charl56/Jukebox-V2/models/V3/Assemblage_cd.SLDASM

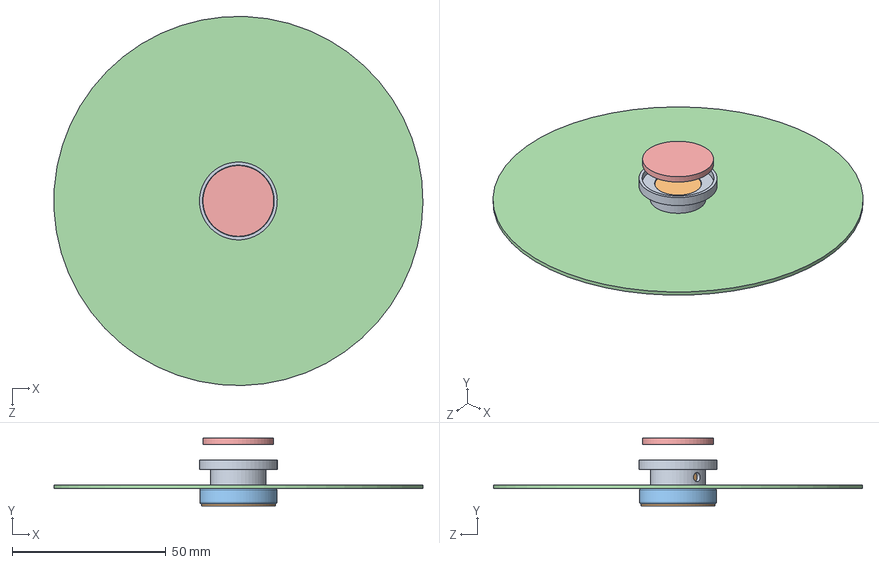
[picture p3: CAD file, 2025-11-25]
models/V3/Assemblage_cd.SLDASM
119.9 x 22.0 x 119.9 mm
Rondelle_prise
Cd_vide
Aimant
Support_cd_dos_aiamant_devant
Bouchon_aiamant_devant
