charl56/Jukebox-V2/models/V3/Assemblage_final.SLDASM

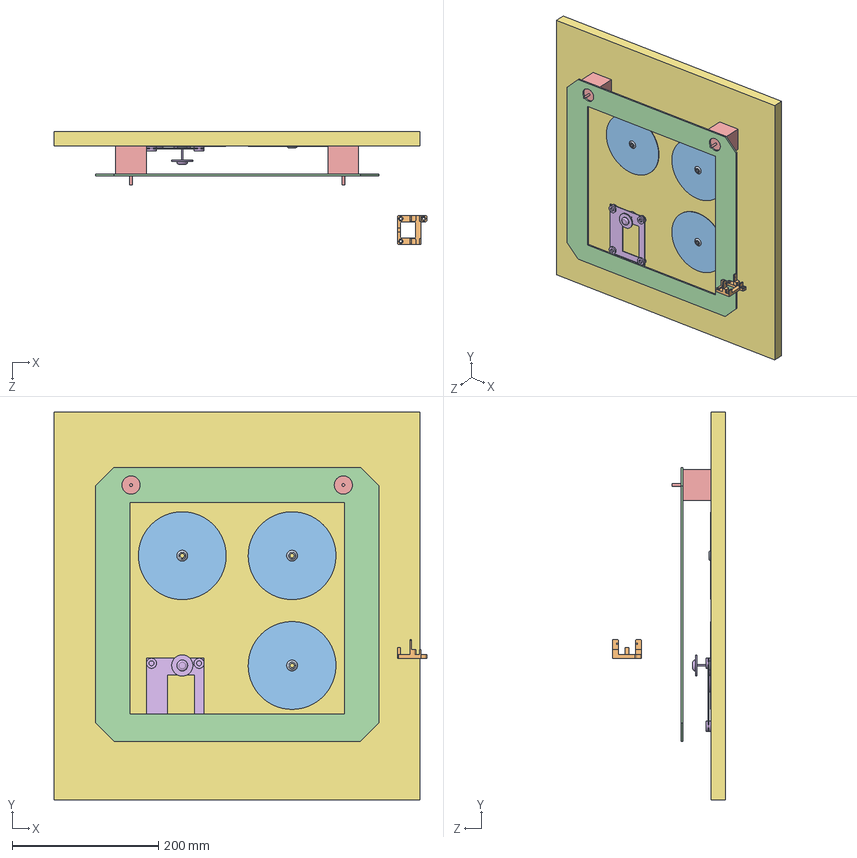
[picture p5: CAD file, 2025-11-25]
models/V3/Assemblage_final.SLDASM
509.1 x 530.0 x 154.8 mm
plaque
lecteur_cd_v2
moteur_pas_a_pas x 2
armature_moteurs
cd x 3
Support_elecaimant
support_cd_mur x 3
