charl56/Jukebox-V2/models/pinion_2.SLDPRT

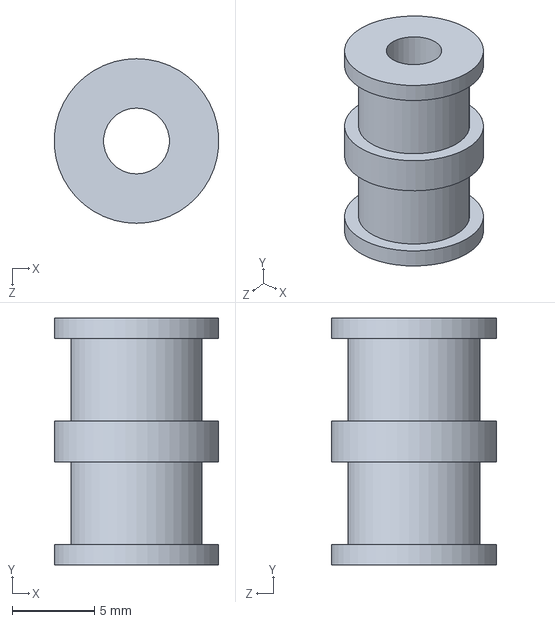
[picture p18: CAD file, 2025-04-08]
models/pinion_2.SLDPRT
9.98 x 15.0 x 10.0 mm
