charl56/Jukebox-V2/3d_models/nacelle_petite.SLDPRT

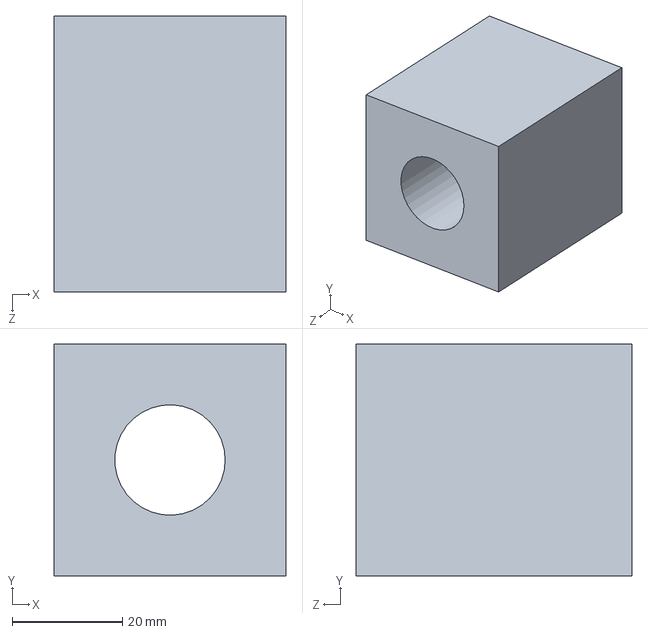
[picture p19: CAD file, 2024-03-14]
3d_models/nacelle_petite.SLDPRT
42.0 x 42.0 x 50.0 mm
