charl56/Jukebox-V2/models/rail.SLDPRT

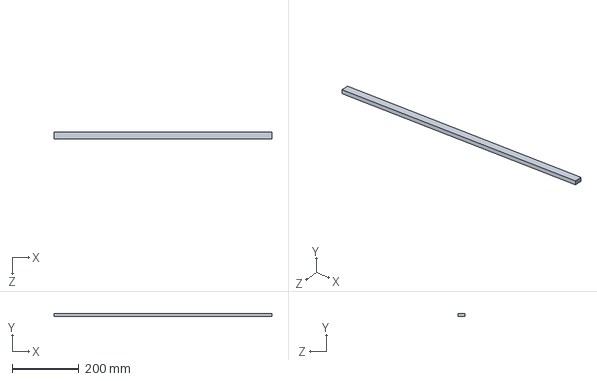
[picture p20: CAD file, 2025-04-08]
models/rail.SLDPRT
655.0 x 10.0 x 20.0 mm
