charl56/Jukebox-V2/models/V3/Bouchon_aiamant_devant.SLDPRT

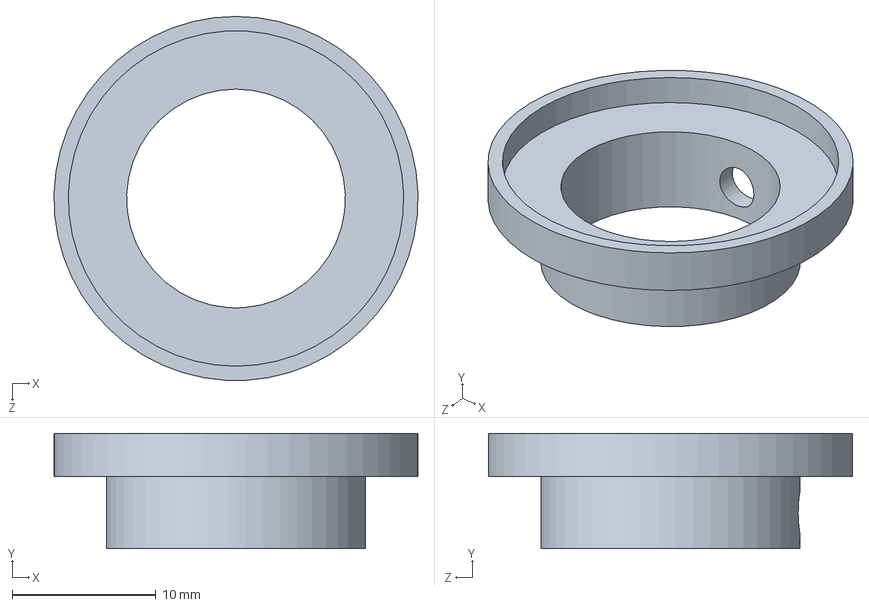
[picture p21: CAD file, 2025-11-25]
models/V3/Bouchon_aiamant_devant.SLDPRT
25.3 x 8.00 x 25.3 mm
