charl56/Jukebox-V2/models/plaque_plexi.SLDPRT

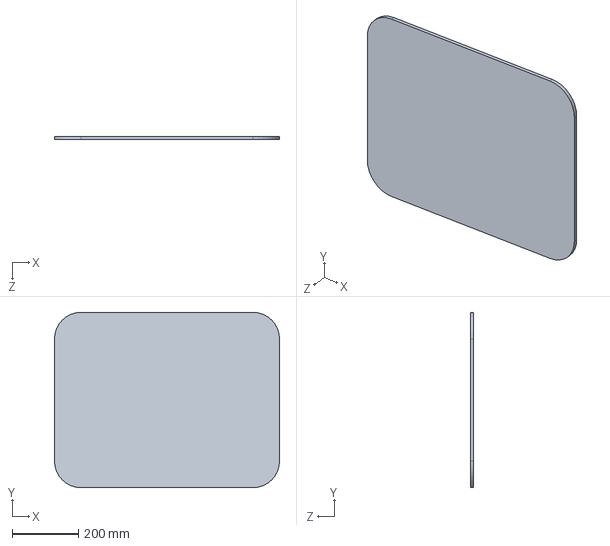
[picture p23: CAD file, 2025-04-08]
models/plaque_plexi.SLDPRT
680.0 x 530.0 x 10.0 mm
