charl56/Jukebox-V2/models/V3/armature_moteurs.SLDPRT

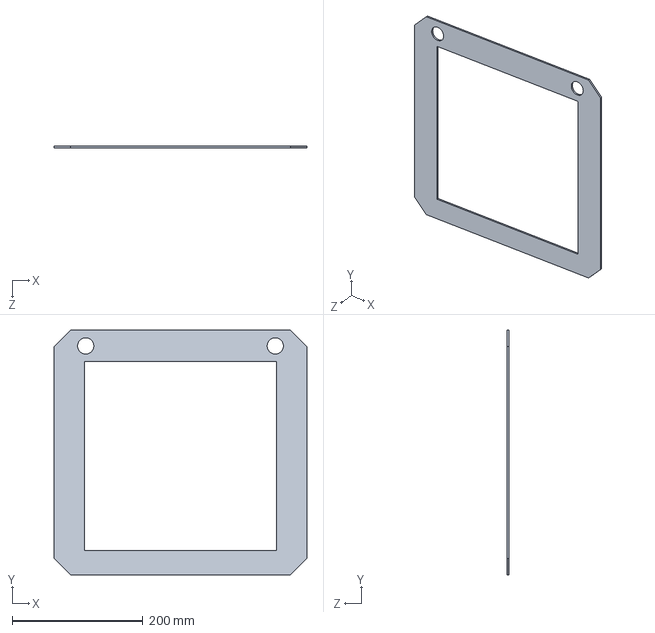
[picture p24: CAD file, 2025-11-25]
models/V3/armature_moteurs.SLDPRT
387.0 x 374.0 x 3.00 mm
