charl56/Jukebox-V2/3d_models/servo_fs90r.SLDPRT

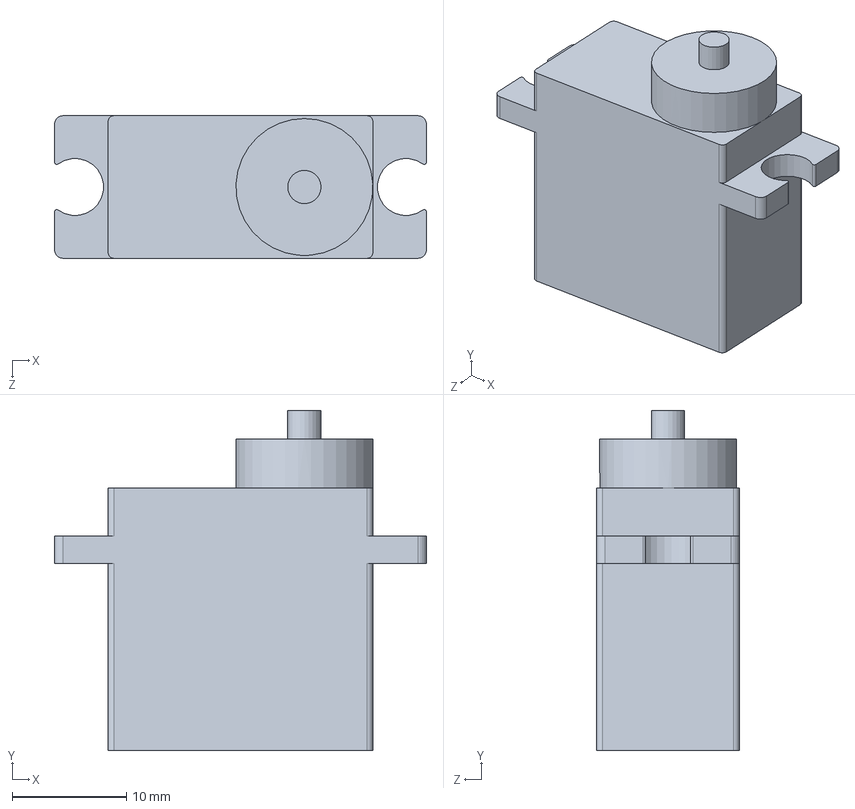
[picture p25: CAD file, 2024-03-14]
3d_models/servo_fs90r.SLDPRT
32.6 x 29.8 x 12.5 mm
