charl56/Jukebox-V2/models/lien_roulement_plateau_moteur_avec_accroches.SLDPRT

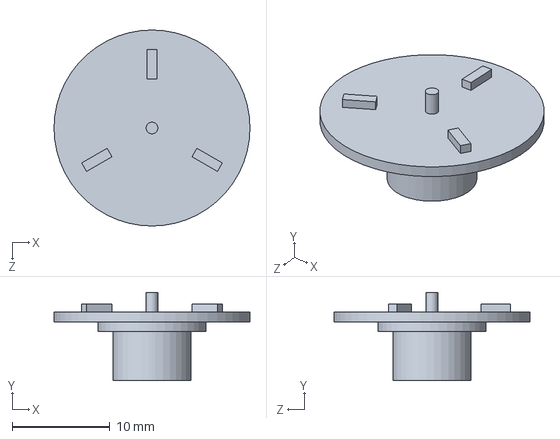
[picture p26: CAD file, 2025-04-08]
models/lien_roulement_plateau_moteur_avec_accroches.SLDPRT
20.0 x 9.00 x 20.0 mm
