charl56/Jukebox-V2/models/V3/support_cd_mur.SLDPRT

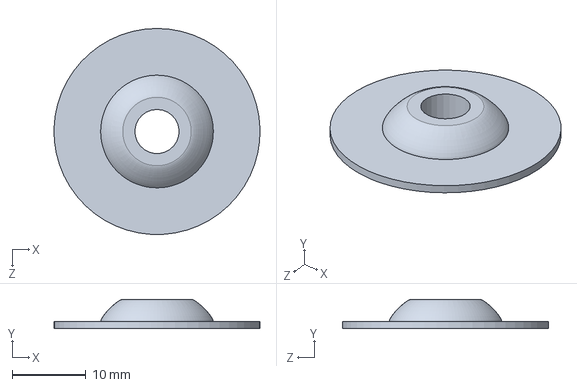
[picture p27: CAD file, 2025-11-25]
models/V3/support_cd_mur.SLDPRT
28.0 x 4.00 x 28.0 mm
