charl56/Jukebox-V2/3d_models/tige_filetee_petite.SLDPRT

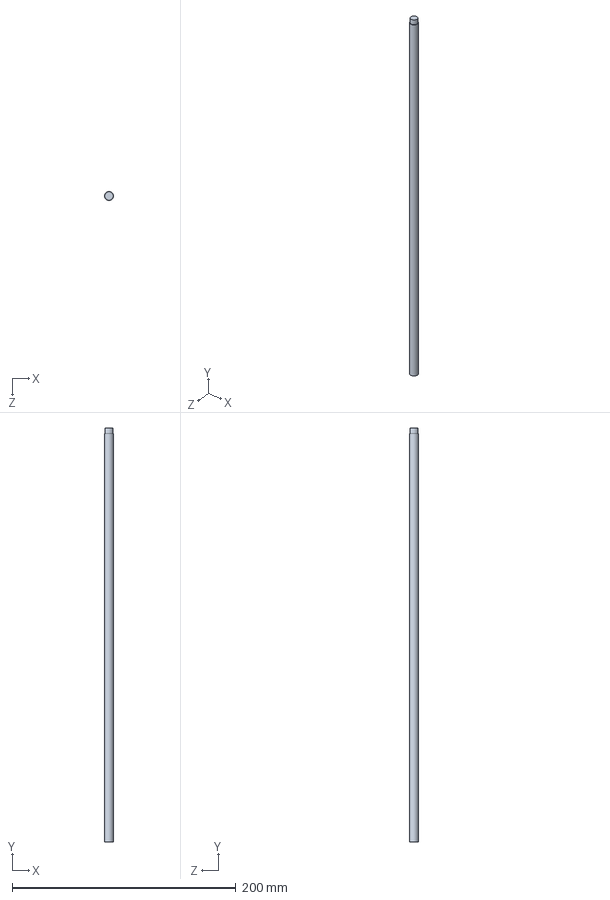
[picture p28: CAD file, 2024-03-14]
3d_models/tige_filetee_petite.SLDPRT
8.00 x 370.0 x 8.00 mm
