charl56/Jukebox-V2/models/lien_roulement_plateau_moteur.SLDPRT

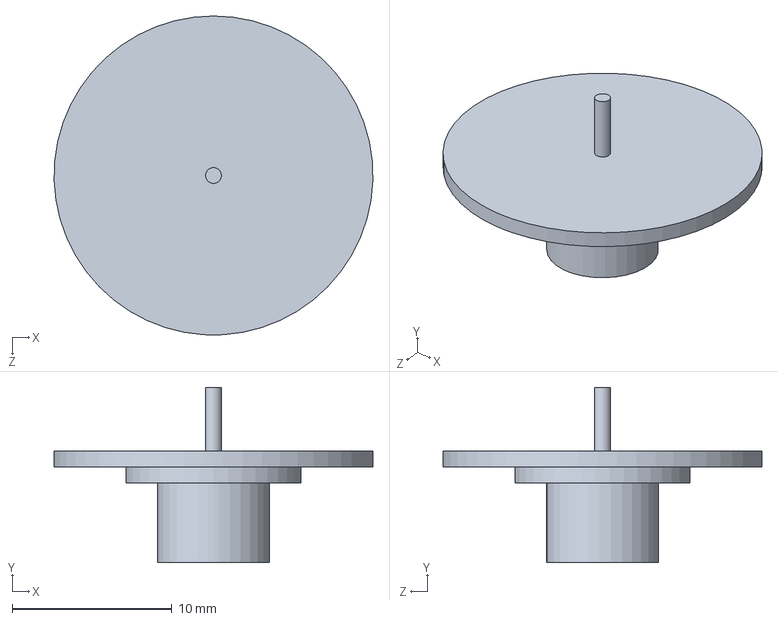
[picture p29: CAD file, 2025-02-26]
models/lien_roulement_plateau_moteur.SLDPRT
20.0 x 11.0 x 20.0 mm
