charl56/Jukebox-V2/models/V3/Cd_vide.SLDPRT

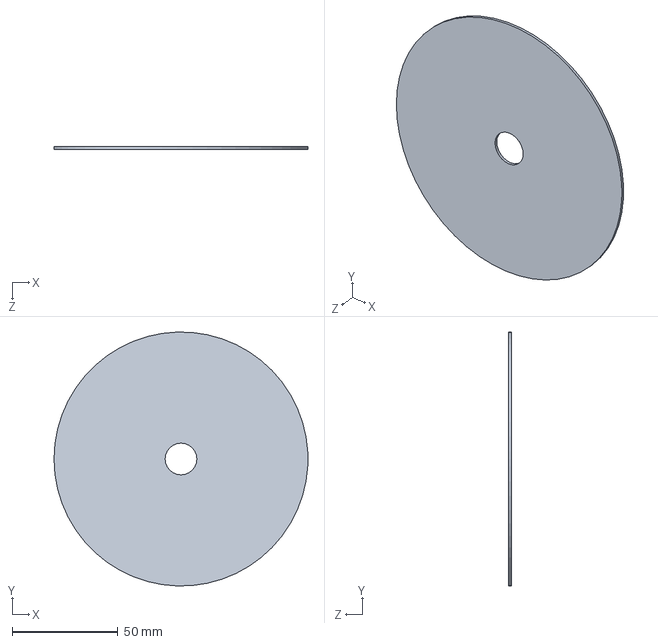
[picture p30: CAD file, 2025-11-25]
models/V3/Cd_vide.SLDPRT
120.0 x 119.9 x 1.20 mm
