charl56/Jukebox-V2/3d_models/pusher_100mm_long.SLDPRT

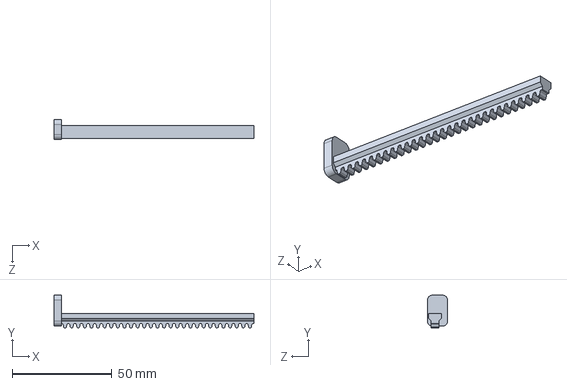
[picture p31: CAD file, 2024-03-14]
3d_models/pusher_100mm_long.SLDPRT
100.0 x 16.3 x 10.2 mm
