charl56/Jukebox-V2/models/cadre_plexi.SLDPRT

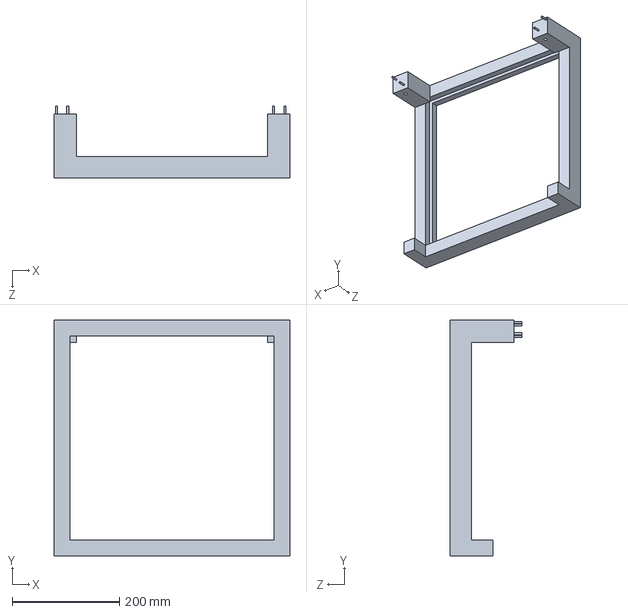
[picture p32: CAD file, 2025-02-26]
models/cadre_plexi.SLDPRT
440.0 x 440.0 x 135.0 mm
