charl56/Jukebox-V2/models/V3/moteur_pas_a_pas.SLDPRT

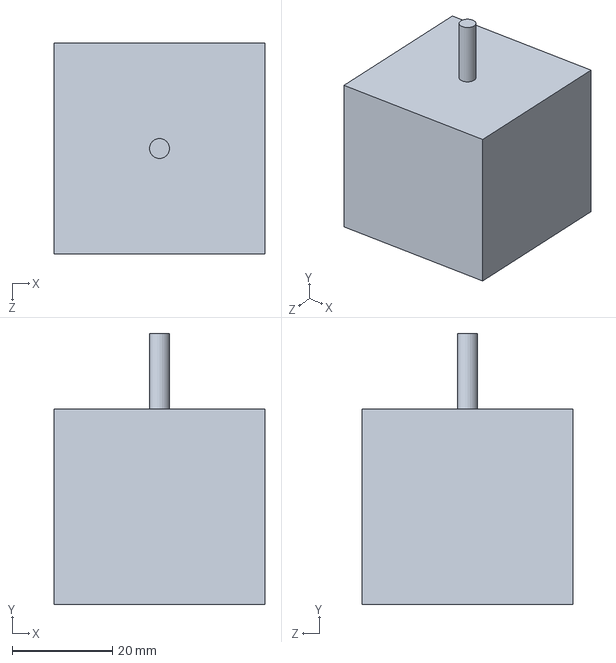
[picture p33: CAD file, 2025-11-25]
models/V3/moteur_pas_a_pas.SLDPRT
42.0 x 54.0 x 42.0 mm
