charl56/Jukebox-V2/3d_models/nacelle_grande_bas.SLDPRT

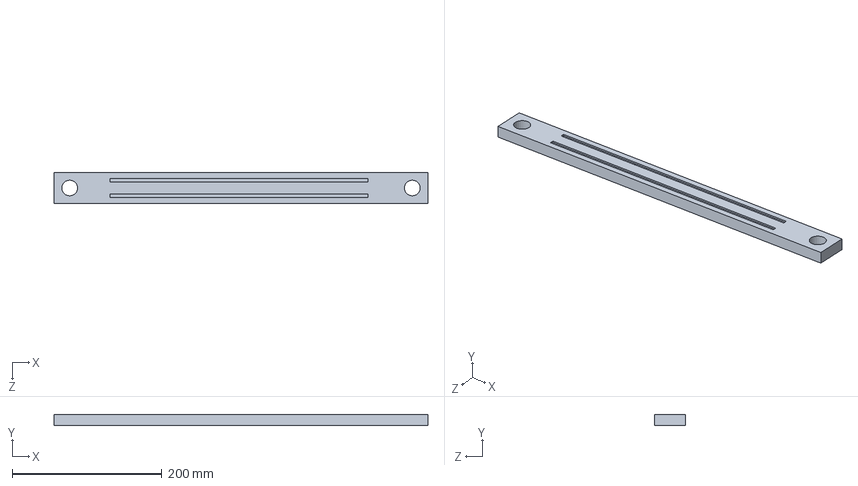
[picture p34: CAD file, 2024-03-14]
3d_models/nacelle_grande_bas.SLDPRT
500.0 x 15.0 x 42.0 mm
