charl56/Jukebox-V2/models/lien_roulement_plaque_plexi.SLDPRT

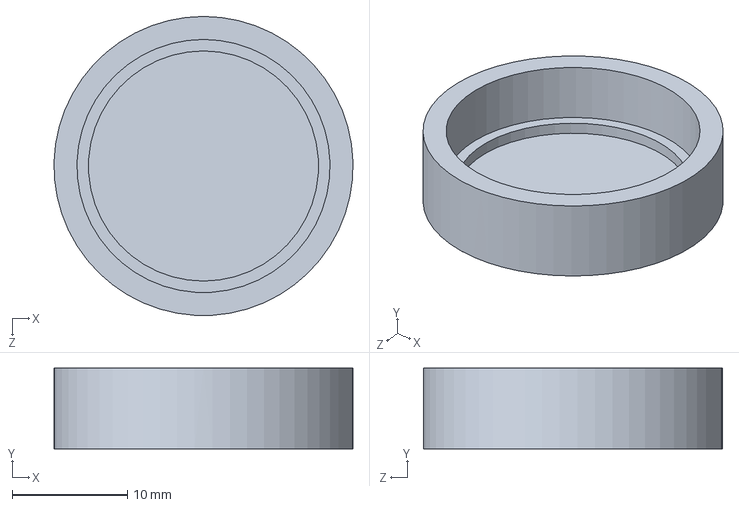
[picture p35: CAD file, 2025-02-26]
models/lien_roulement_plaque_plexi.SLDPRT
26.0 x 7.00 x 26.0 mm
