charl56/Jukebox-V2/models/V3/Aimant.SLDPRT

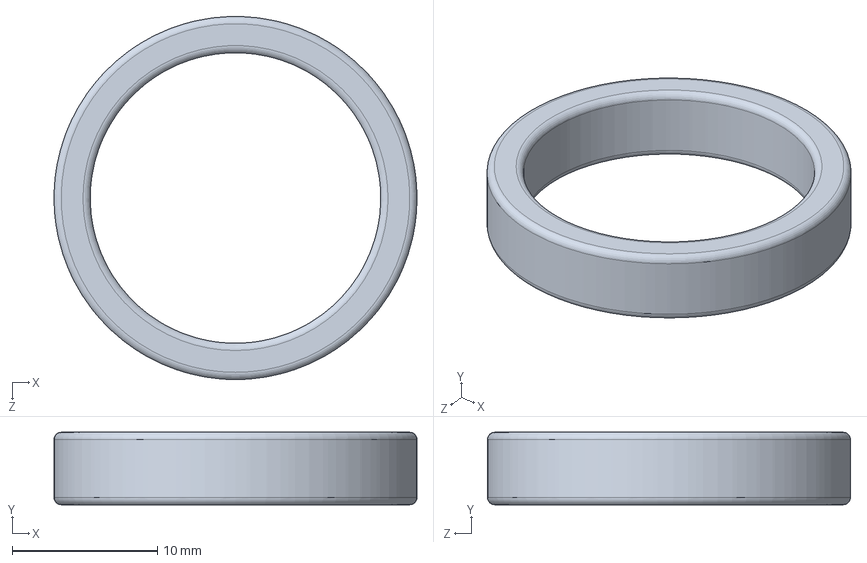
[picture p36: CAD file, 2025-11-25]
models/V3/Aimant.SLDPRT
25.0 x 5.00 x 25.0 mm
