charl56/Jukebox-V2/3d_models/nacelle_grande_haut.SLDPRT

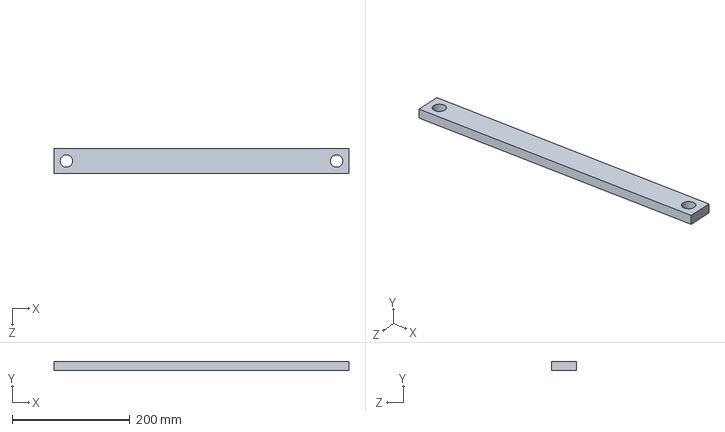
[picture p37: CAD file, 2024-03-14]
3d_models/nacelle_grande_haut.SLDPRT
500.0 x 15.0 x 42.0 mm
