charl56/Jukebox-V2/models/pinion_gear_mini.SLDPRT

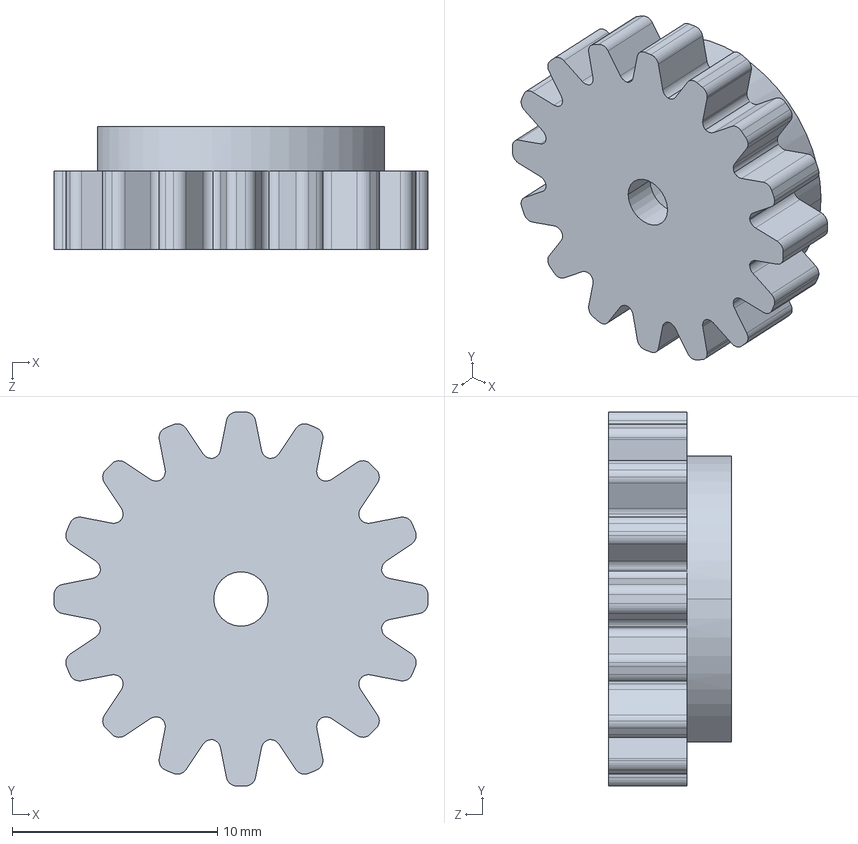
[picture p38: CAD file, 2025-02-14]
models/pinion_gear_mini.SLDPRT
18.2 x 18.2 x 5.97 mm
