charl56/Jukebox-V2/models/V3/Rondelle_prise.SLDPRT

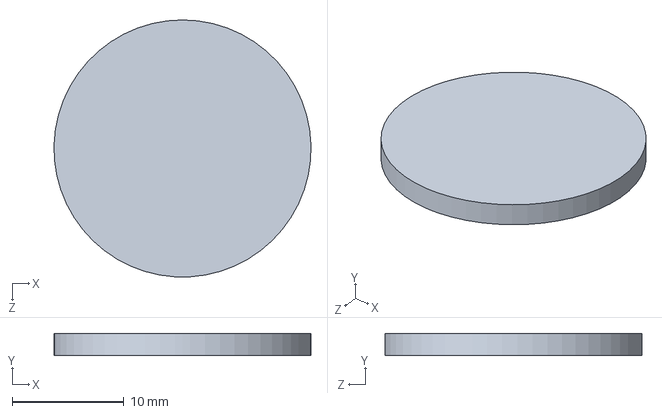
[picture p39: CAD file, 2025-11-25]
models/V3/Rondelle_prise.SLDPRT
23.0 x 2.00 x 23.0 mm
