charl56/Jukebox-V2/3d_models/pusher_125mm.SLDPRT

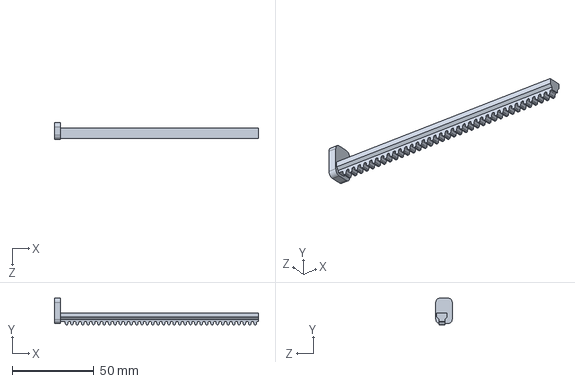
[picture p40: CAD file, 2024-03-14]
3d_models/pusher_125mm.SLDPRT
125.0 x 16.3 x 10.2 mm
