charl56/Jukebox-V2/models/cd.SLDPRT

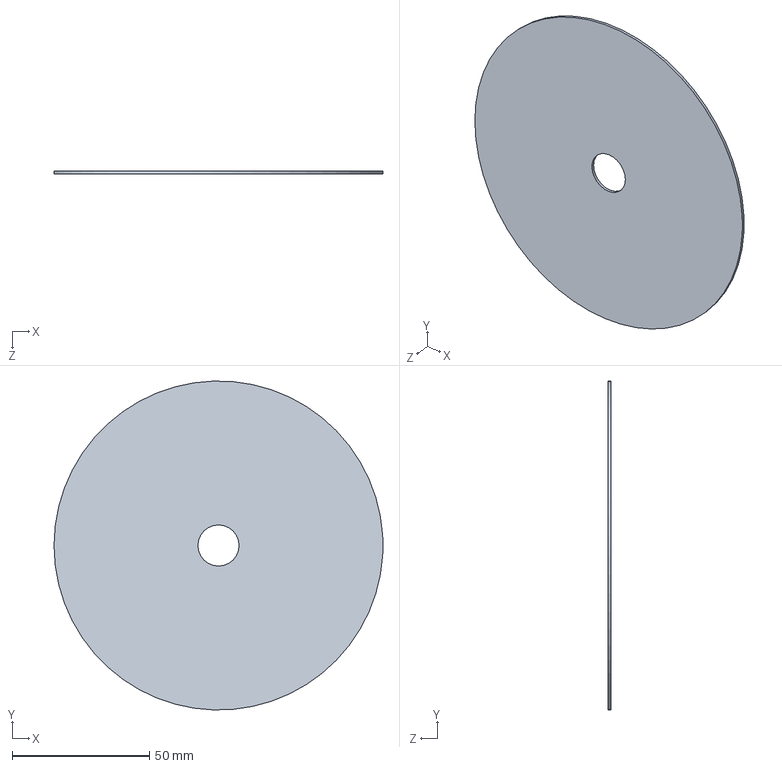
[picture p41: CAD file, 2025-02-14]
models/cd.SLDPRT
120.0 x 119.9 x 1.00 mm
