charl56/Jukebox-V2/models/V3/Pièce3.STL

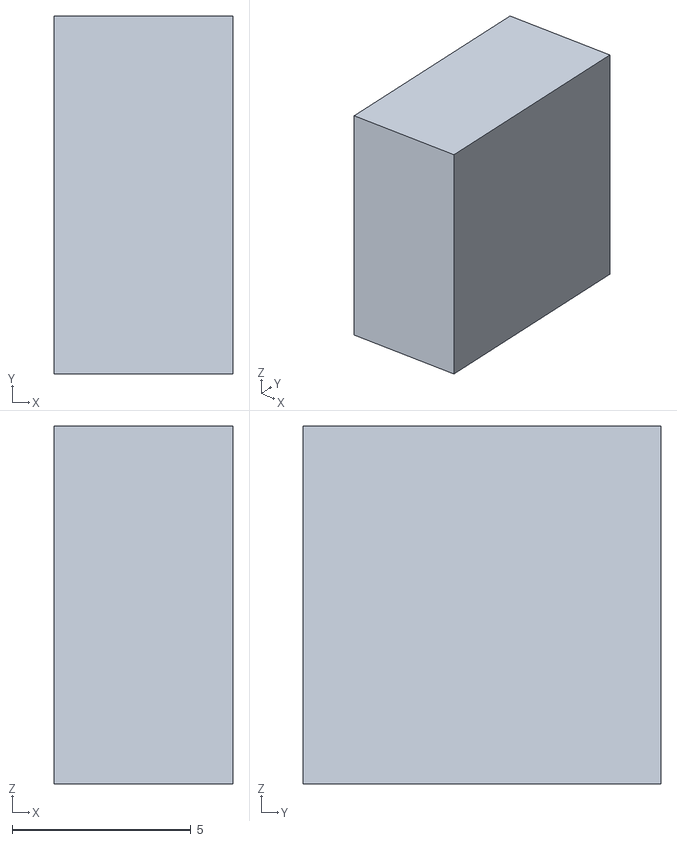
[picture p42: CAD file, 2025-11-25]
models/V3/Pièce3.STL
5.00 x 10.0 x 10.0
