charl56/Jukebox-V2/3d_models/motor bracket, mini version.SLDPRT

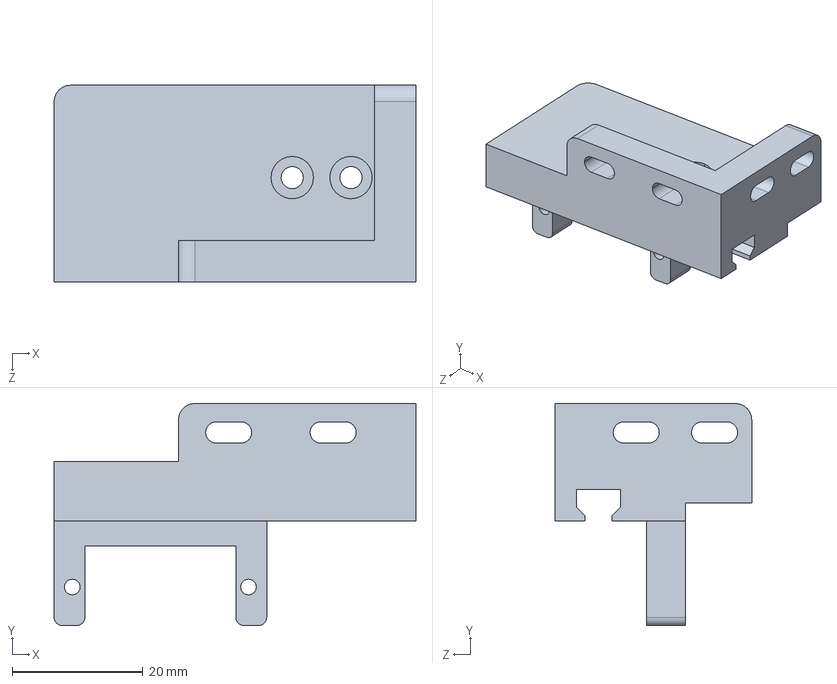
[picture p43: CAD file, 2024-03-14]
3d_models/motor bracket, mini version.SLDPRT
55.5 x 34.0 x 30.1 mm
