charl56/Jukebox-V2/3d_models/lecteur_cd.SLDPRT

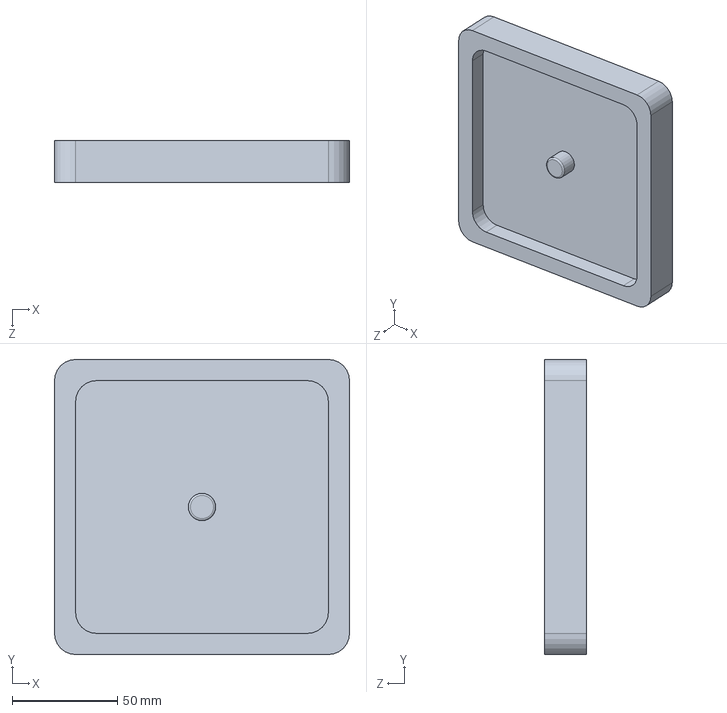
[picture p45: CAD file, 2024-03-14]
3d_models/lecteur_cd.SLDPRT
140.0 x 140.0 x 20.0 mm
