charl56/Jukebox-V2/models/lecteur_cd_v3_avec_support.SLDPRT

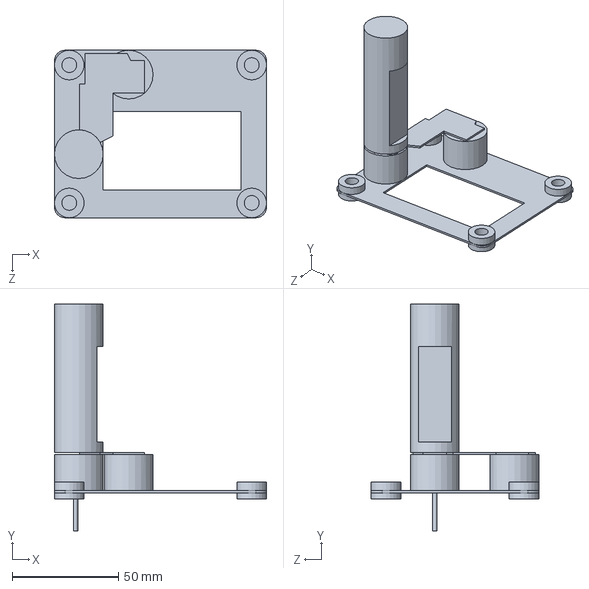
[picture p46: CAD file, 2025-02-14]
models/lecteur_cd_v3_avec_support.SLDPRT
100.0 x 107.0 x 79.0 mm
