charl56/Jukebox-V2/3d_models/tige_depl_x.SLDPRT

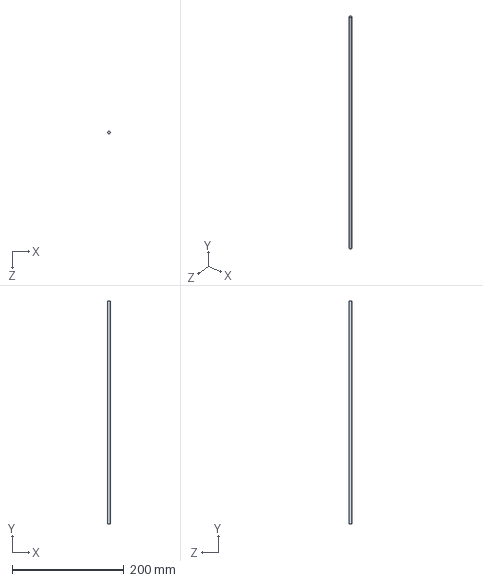
[picture p47: CAD file, 2024-03-14]
3d_models/tige_depl_x.SLDPRT
5.00 x 400.0 x 5.00 mm
