charl56/Jukebox-V2/models/roulement_billes.SLDPRT

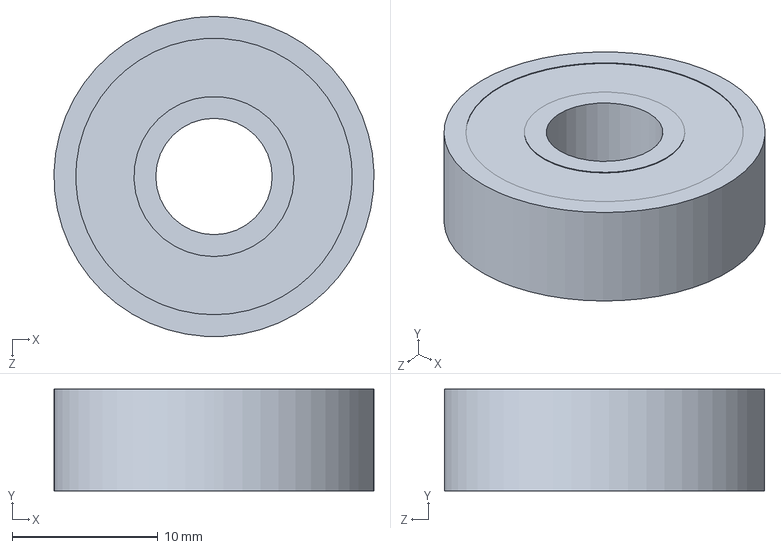
[picture p48: CAD file, 2025-02-14]
models/roulement_billes.SLDPRT
22.0 x 7.00 x 22.0 mm
