charl56/Jukebox-V2/3d_models/depl_x.SLDPRT

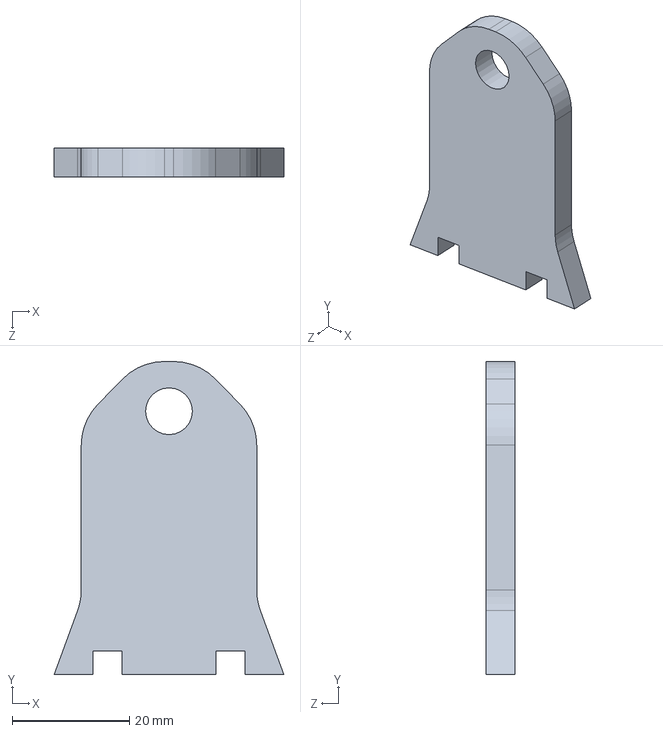
[picture p49: CAD file, 2024-03-14]
3d_models/depl_x.SLDPRT
39.3 x 53.5 x 5.00 mm
