charl56/Jukebox-V2/models/support_nacelle_v2_courroies.SLDPRT

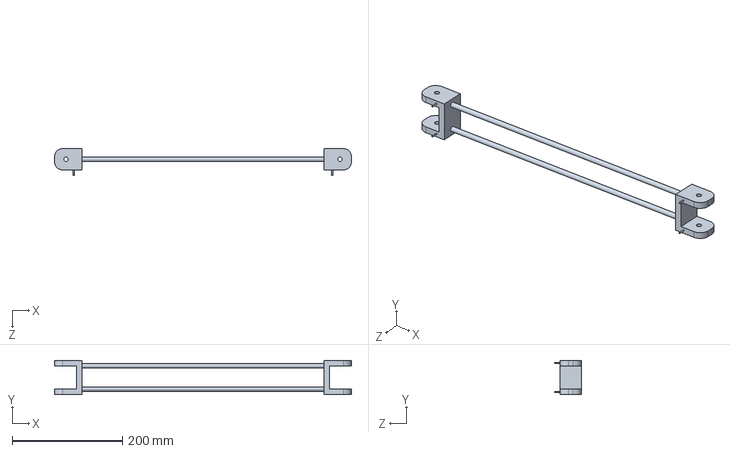
[picture p50: CAD file, 2025-02-14]
models/support_nacelle_v2_courroies.SLDPRT
540.0 x 62.0 x 49.0 mm
