charl56/Jukebox-V2/3d_models/ecrou_nacelle.SLDPRT

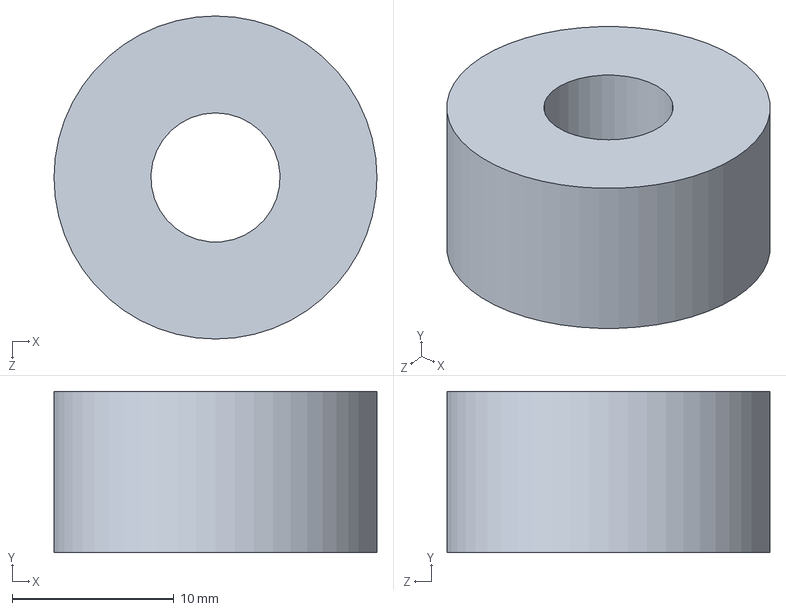
[picture p51: CAD file, 2024-03-14]
3d_models/ecrou_nacelle.SLDPRT
20.0 x 10.0 x 20.0 mm
