charl56/Jukebox-V2/models/plateau_moteur_lecteur.SLDPRT

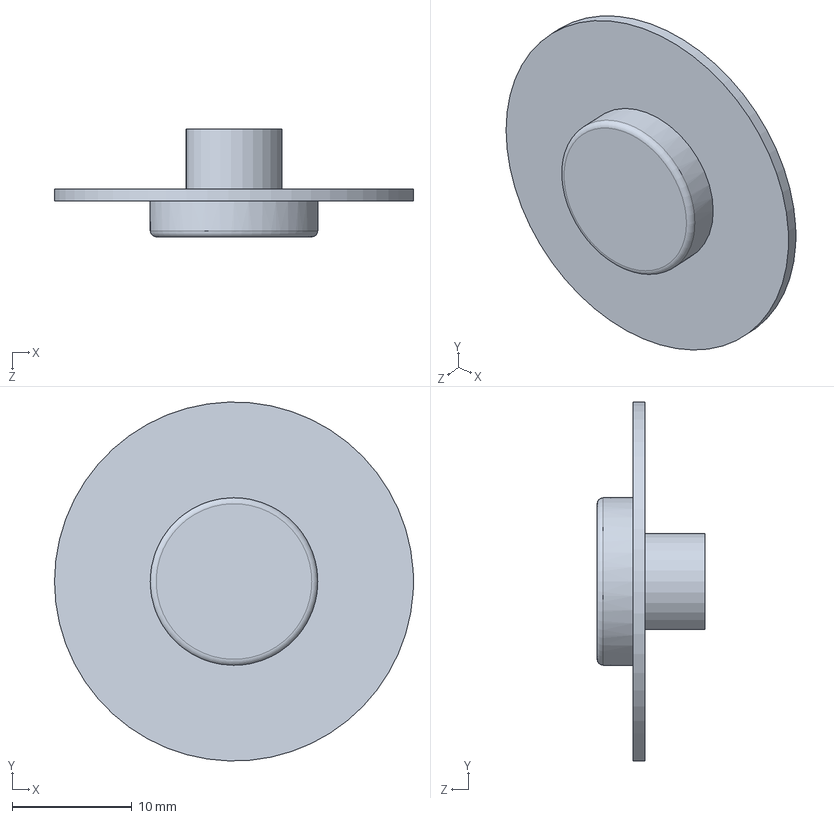
[picture p52: CAD file, 2025-02-14]
models/plateau_moteur_lecteur.SLDPRT
30.0 x 30.0 x 9.00 mm
