charl56/Jukebox-V2/3d_models/support_cd.SLDPRT

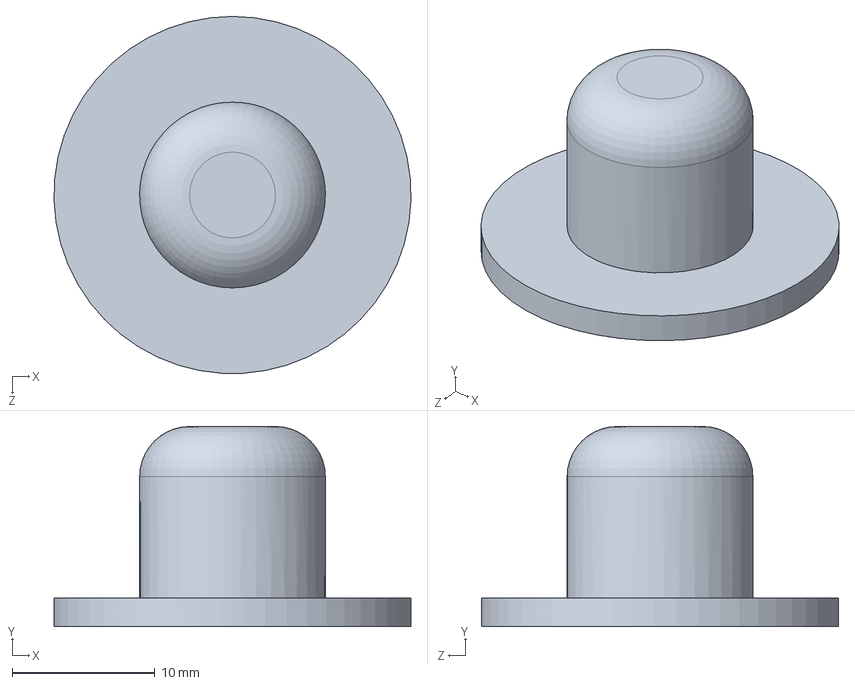
[picture p53: CAD file, 2024-02-16]
3d_models/support_cd.SLDPRT
25.0 x 14.0 x 25.0 mm
