charl56/Jukebox-V2/models/fin_de_course_basGrand.SLDPRT

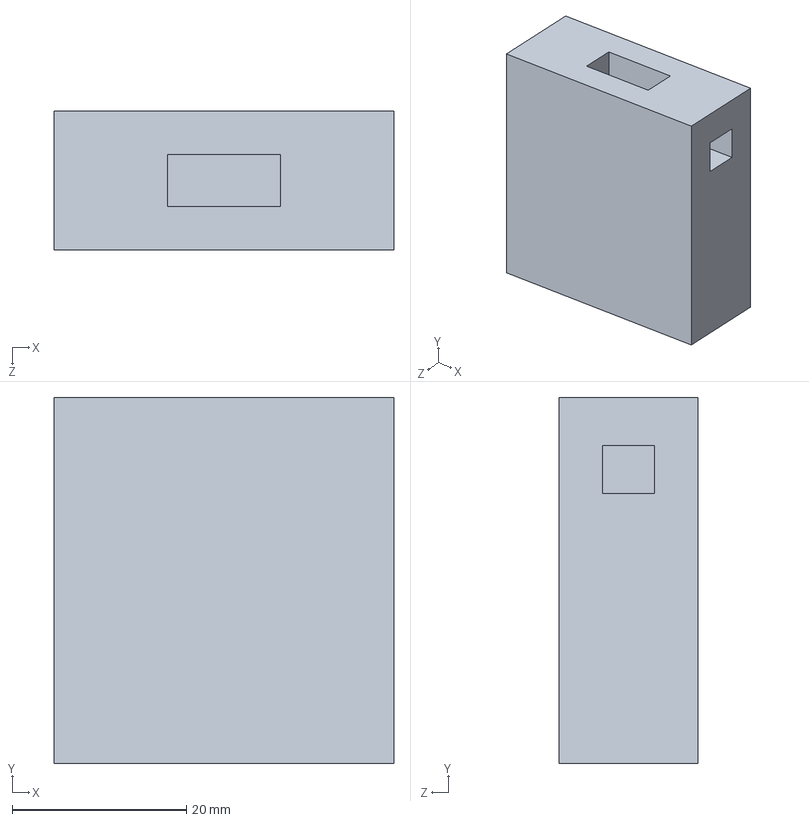
[picture p54: CAD file, 2025-02-14]
models/fin_de_course_basGrand.SLDPRT
39.0 x 42.0 x 16.0 mm
