charl56/Jukebox-V2/models/nacelle_grande_hautGrand.SLDPRT

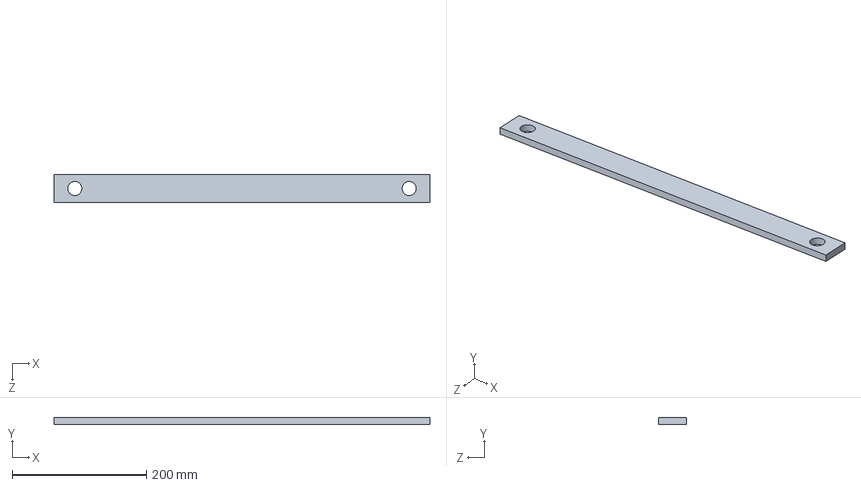
[picture p55: CAD file, 2025-02-14]
models/nacelle_grande_hautGrand.SLDPRT
560.0 x 10.0 x 42.0 mm
