charl56/Jukebox-V2/models/nacelle_v2.SLDPRT

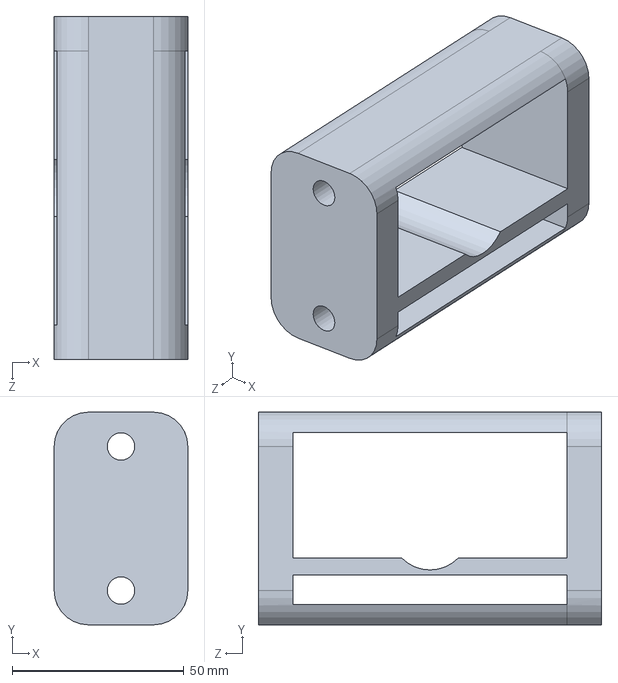
[picture p56: CAD file, 2025-02-14]
models/nacelle_v2.SLDPRT
39.0 x 62.0 x 100.0 mm
