charl56/Jukebox-V2/models/support_nacelle_cote_gauche.SLDPRT

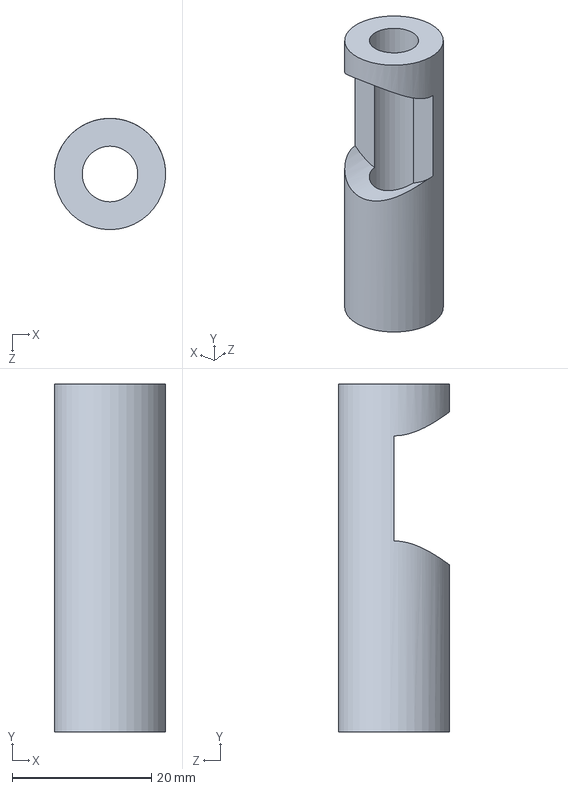
[picture p57: CAD file, 2025-02-14]
models/support_nacelle_cote_gauche.SLDPRT
16.0 x 50.0 x 16.0 mm
