charl56/Jukebox-V2/models/socleGrand.SLDPRT

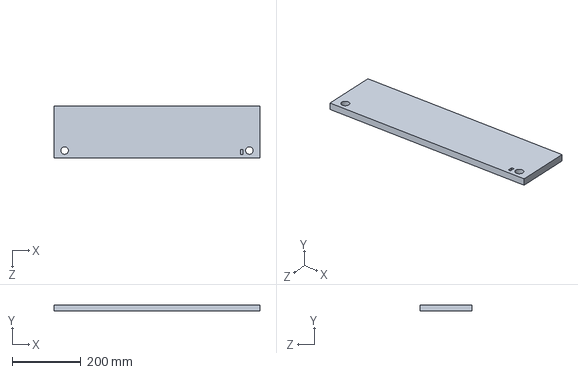
[picture p58: CAD file, 2024-10-30]
models/socleGrand.SLDPRT
600.0 x 18.0 x 150.0 mm
