charl56/Jukebox-V2/models/motor_bracket_mini_2.SLDPRT

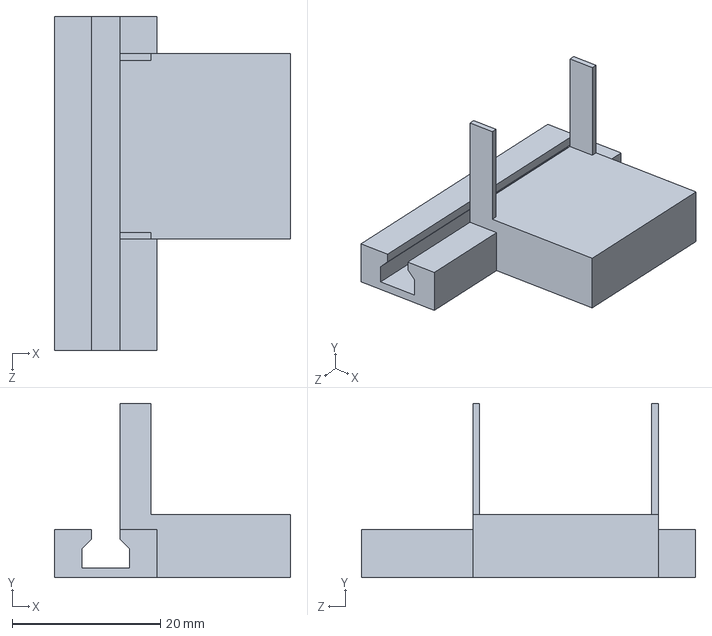
[picture p59: CAD file, 2024-10-30]
models/motor_bracket_mini_2.SLDPRT
31.8 x 23.5 x 45.0 mm
