charl56/Jukebox-V2/models/support_roulements.SLDPRT

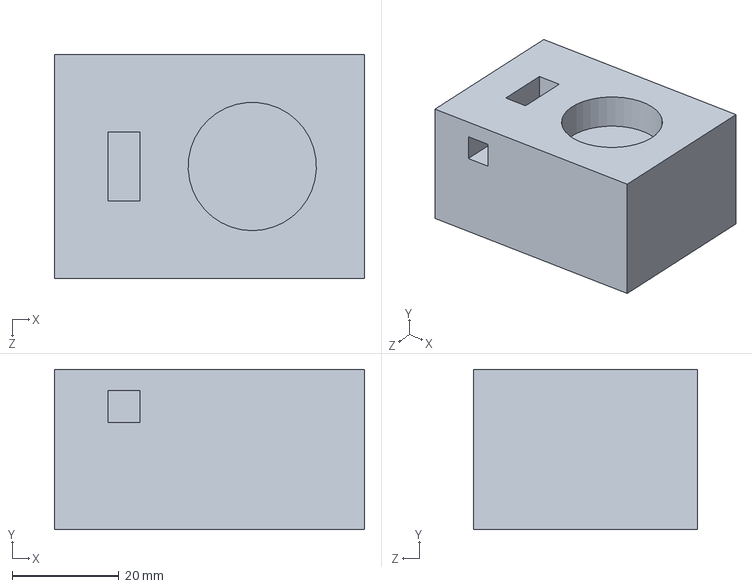
[picture p60: CAD file, 2024-10-30]
models/support_roulements.SLDPRT
58.0 x 30.0 x 42.0 mm
