charl56/Jukebox-V2/models/tige_filetee_petiteGrand.SLDPRT

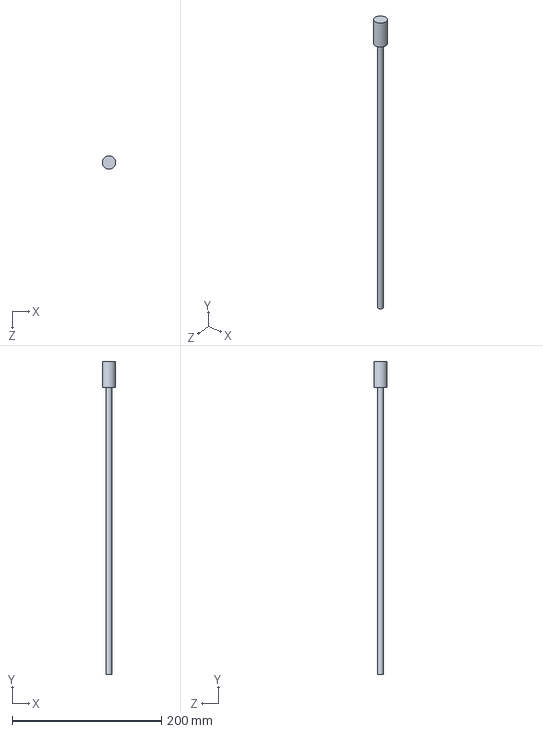
[picture p61: CAD file, 2024-10-30]
models/tige_filetee_petiteGrand.SLDPRT
18.0 x 420.0 x 18.0 mm
