charl56/Jukebox-V2/models/nacelle_aimant.SLDPRT

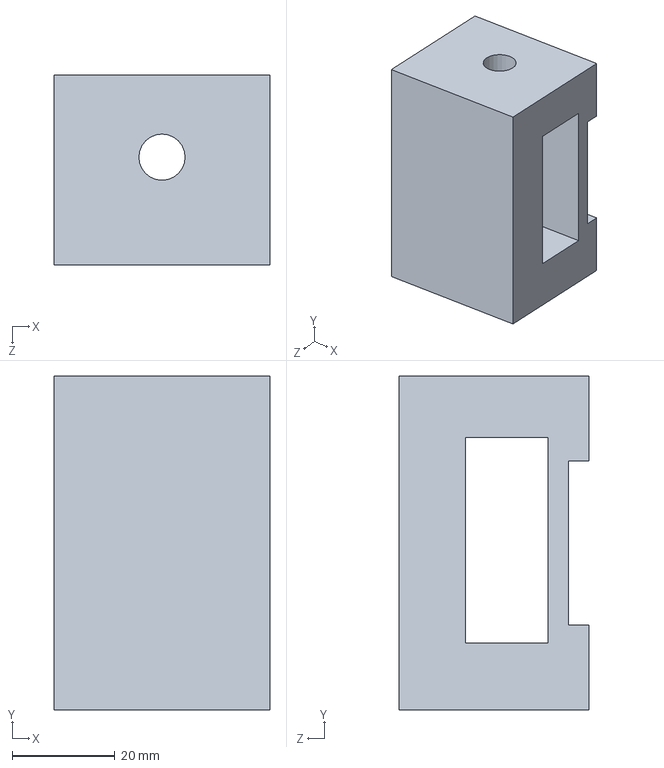
[picture p62: CAD file, 2024-10-30]
models/nacelle_aimant.SLDPRT
42.0 x 65.0 x 37.0 mm
