charl56/Jukebox-V2/models/fin_de_course_bas.SLDPRT

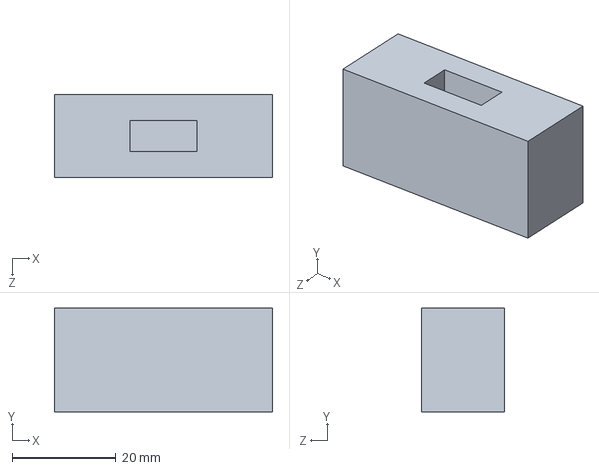
[picture p63: CAD file, 2024-07-17]
models/fin_de_course_bas.SLDPRT
42.0 x 20.0 x 16.0 mm
