charl56/Jukebox-V2/models/electroaimant.SLDPRT

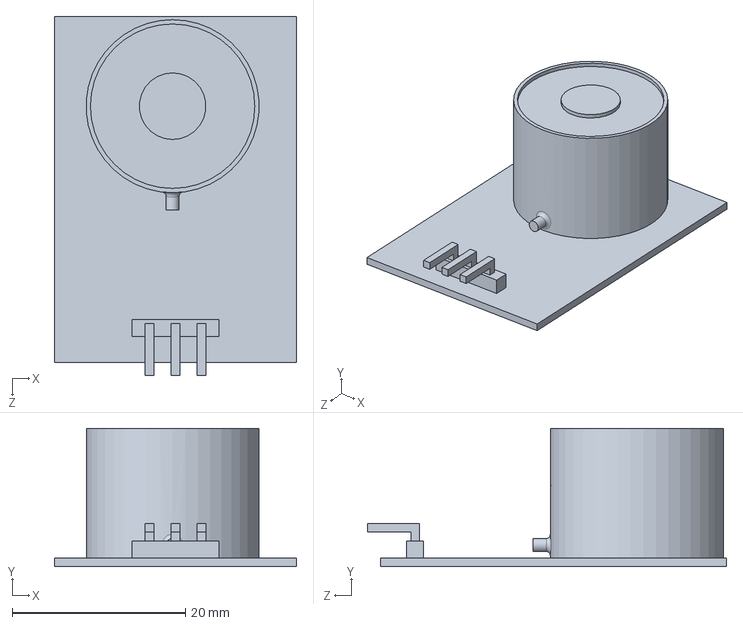
[picture p64: CAD file, 2024-07-17]
models/electroaimant.SLDPRT
28.0 x 16.0 x 41.5 mm
