charl56/Jukebox-V2/models/nacelle_grande_basGrand.SLDPRT

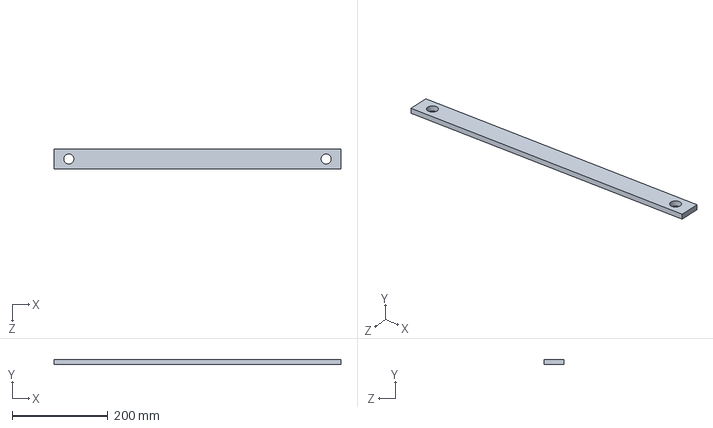
[picture p65: CAD file, 2024-07-17]
models/nacelle_grande_basGrand.SLDPRT
600.0 x 10.0 x 42.0 mm
