charl56/Jukebox-V2/models/plaqueGrande.SLDPRT

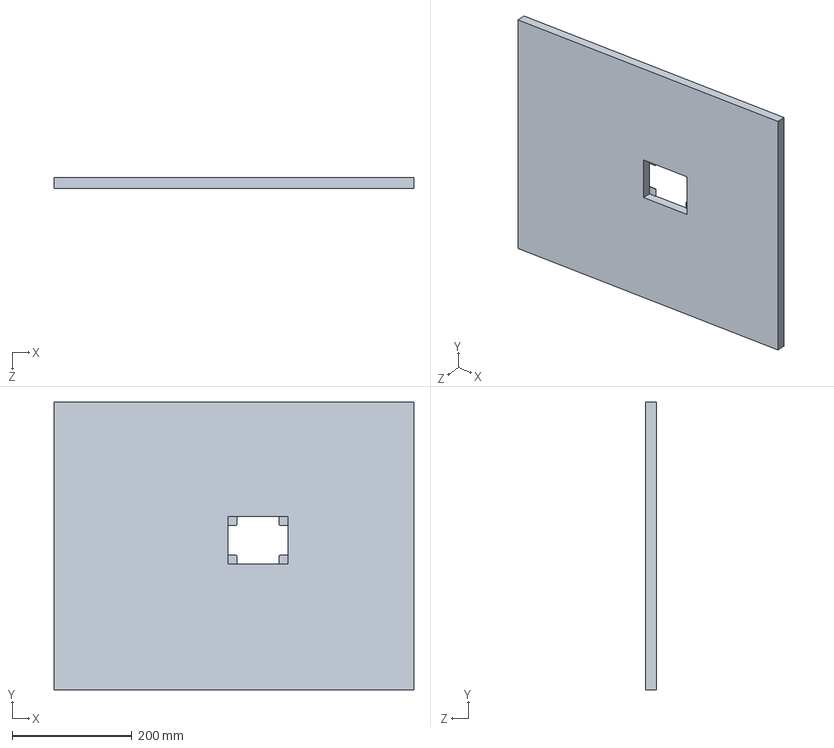
[picture p66: CAD file, 2024-07-17]
models/plaqueGrande.SLDPRT
600.0 x 480.0 x 18.0 mm
