charl56/Jukebox-V2/models/capteur_fin_de_course.SLDPRT

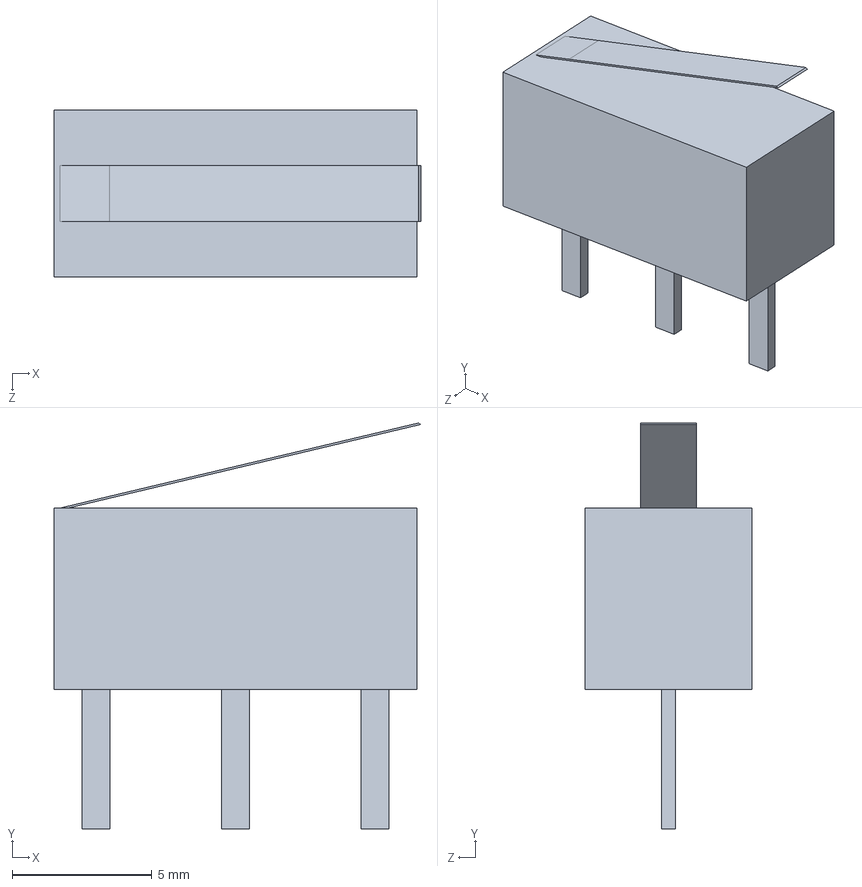
[picture p67: CAD file, 2024-07-16]
models/capteur_fin_de_course.SLDPRT
13.1 x 14.6 x 6.00 mm
