charl56/Jukebox-V2/models/socleBasGrand.SLDPRT

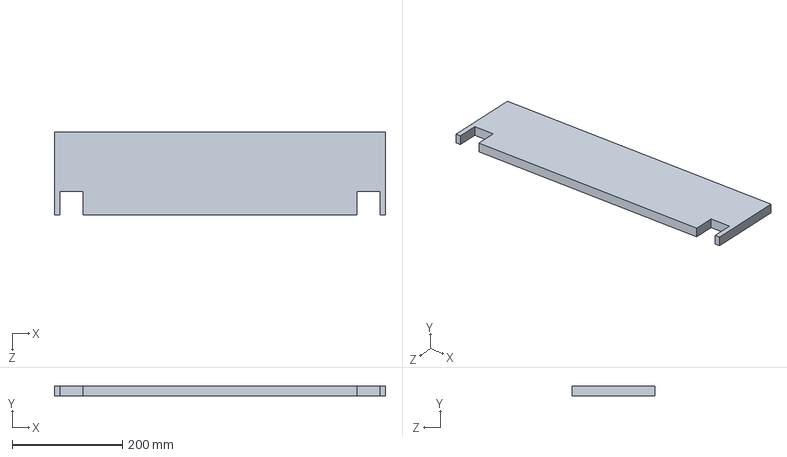
[picture p68: CAD file, 2024-07-14]
models/socleBasGrand.SLDPRT
600.0 x 18.0 x 150.0 mm
