charl56/Jukebox-V2/models/Assemblage2.SLDASM

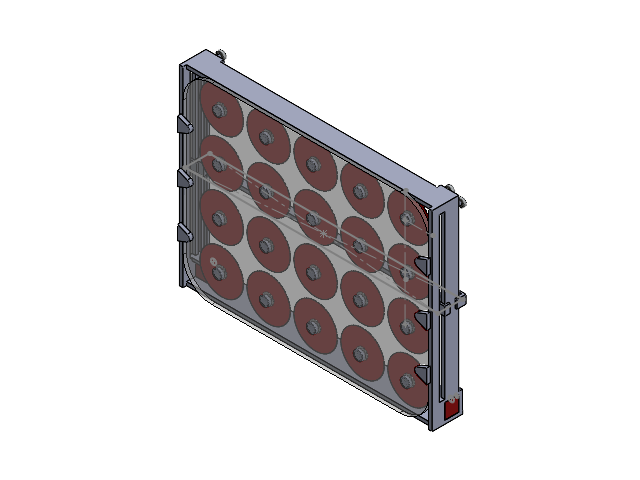
[picture p70: CAD file, 2025-11-25]
models/Assemblage2.SLDASM
plaque_plexi
cd x 20
lien_roulement_plaque_plexi x 20
roulement_billes x 26
lien_roulement_plateau_moteur_avec_accroches x 20
plateau_moteur_lecteur x 20
socle2
servo_moteur x 2
pinion_gear_mini
support_nacelle x 2
rail
pinion_2
