charl56/Jukebox-V2/3d_models/Assemblage.SLDASM

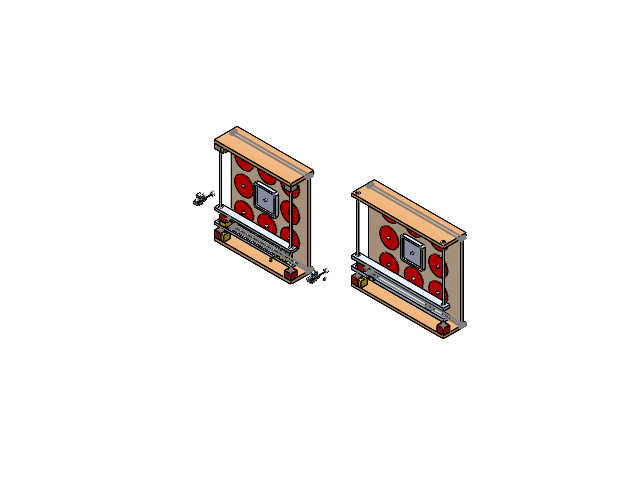
[picture p71: CAD file, 2024-07-14]
3d_models/Assemblage.SLDASM
plaque
support_cd x 16
cd x 16
lecteur_cd x 2
socle x 2
servo_moteur x 6
tige_filetee x 4
support_roulements x 4
roulement_billes x 4
ecrou_nacelle x 8
nacelle_grande_bas
nacelle_grande_haut
fin_de_course_bas x 2
fin_de_course_haut
tige_filetee_petite
motor_bracket_mini x 2
electroaimant x 2
pusher_100mm_long x 4
support_tige_depl_x x 2
depl_x x 2
servo_fs90r x 4
pinion_gear_mini x 2
motor_bracket_mini_2 x 2
depl_x_gauche x 2
nacelle_grande_hautGrand
tige_filetee_petiteGrand
nacelle_grande_basGrand
plaqueGrande
socleGrand x 2
