charl56/Jukebox-V2/backend/routes/data_routes.py

# routes/data_routes.py
import os
from flask import Blueprint, jsonify, request
from utils import load_json_file, save_json_file
import shutil

data_bp = Blueprint('data', __name__)
data_path = './static/data.json'
empty_data_path = './static/data_empty.json'


@data_bp.route('/cd', methods=['GET'])
def get_data():
    try:
        if not os.path.exists(data_path):
            print("pas fichier")
            shutil.copy(empty_data_path, data_path)
            print("copie fichier")

        data = load_json_file(data_path)

        return jsonify({"success": True, "data": data}), 200
    except Exception as e:
        return jsonify({"success": False, "error": str(e)}), 500

@data_bp.route('/cd', methods=['POST'])
def sync_data():
    try:
        data = request.json['data']
        save_json_file(data_path, data)
        return jsonify({"success": True}), 200
    except Exception as e:
        return jsonify({"success": False, "error": str(e)}), 500

@data_bp.route('/image', methods=['POST'])
def upload_file():
    if 'file' not in request.files or 'fileName' not in request.form:
        return jsonify({"success": False, "error": "No file or picture name part"}), 400

    file = request.files['file']
    picture_name = request.form['fileName']

    if file.filename == '':
        return jsonify({"success": False, "error": "No selected file"}), 400

    file.save(os.path.join('./static/albums/', picture_name))
    return jsonify({"success": True}), 200



@data_bp.route('/image/<fileName>', methods=['PUT'])
def rename_file(fileName):
    newFileName = request.json['newFileName']
    file_path = os.path.join('./static/albums/' + fileName + '.webp')
    new_file_path = os.path.join('./static/albums/' + newFileName + '.webp')
    
    # Vérifier si le fichier source existe
    if not os.path.exists(file_path):
        return jsonify({"error": "Le fichier source n'existe pas"}), 404
    
    # Vérifier si le nouveau nom de fichier existe déjà
    if os.path.exists(new_file_path):
        return jsonify({"error": "Un fichier avec ce nom existe déjà"}), 409
    
    try:
        # Renommer le fichier
        os.rename(file_path, new_file_path)
        return jsonify({"success": True, "newPath": new_file_path}), 200
    except Exception as e:
        return jsonify({"error": str(e)}), 500



@data_bp.route('/image/<fileName>', methods=['DELETE'])
def delete_file(fileName):

    file_path = os.path.join('./static/albums/' + fileName + '.webp')

    if not os.path.exists(file_path):
        return jsonify({"success": False, "error": "File not found"}), 404
    
    try:
        os.remove(file_path)
    except Exception as e:
        return jsonify({"success": False, "error": str(e)}), 500

    return jsonify({"success": True}), 200
